IRL-CT/tiltybot/assets/2motormode_ip.png

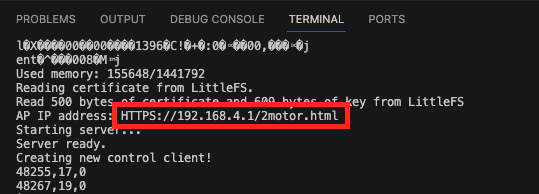
assets/2motormode_ip.png
